Jerry744/halfmind-flow/capsule/structure_hat_v3 v1(Mirror).step

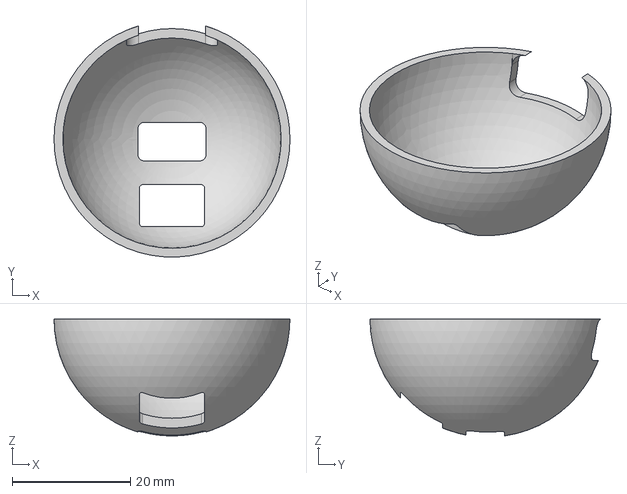
[picture p17: CAD file, 2025-07-03]
capsule/structure_hat_v3 v1(Mirror).step
40.0 x 39.1 x 19.8 mm
