Jerry744/halfmind-flow/capsule/structure_v1_shell.stp

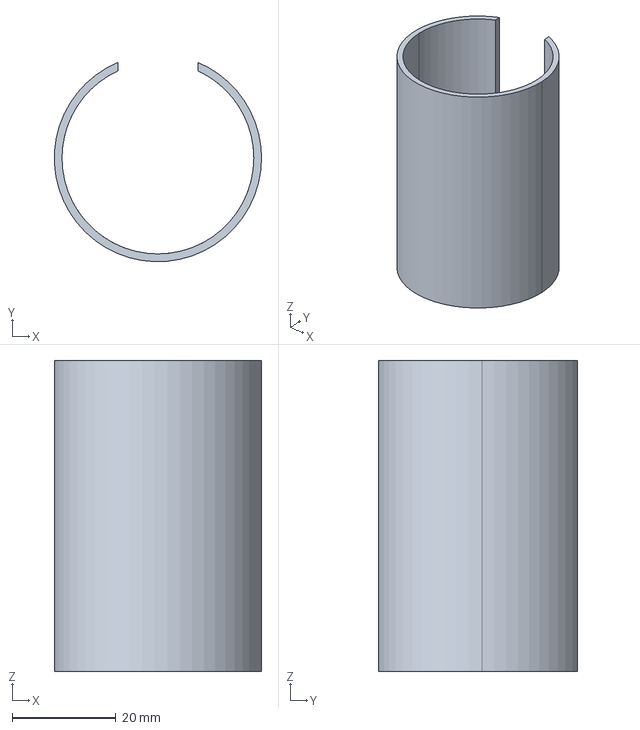
[picture p18: CAD file, 2025-07-01]
capsule/structure_v1_shell.stp
40.0 x 38.4 x 60.0 mm
