Jerry744/halfmind-flow/capsule/structure_hat_v3.stp

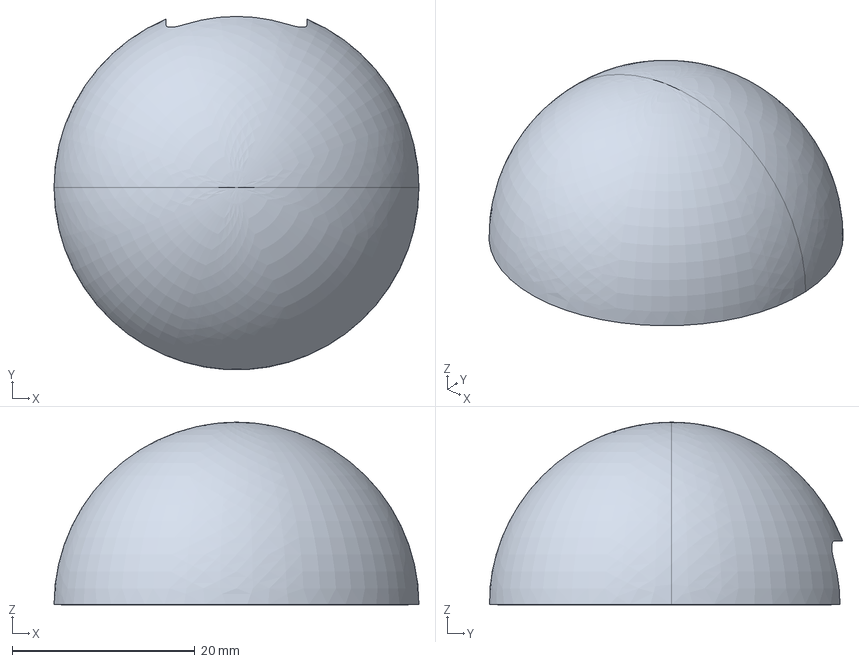
[picture p19: CAD file, 2025-07-01]
capsule/structure_hat_v3.stp
40.0 x 38.7 x 20.0 mm
