Jerry744/halfmind-flow/capsule/radar.stp

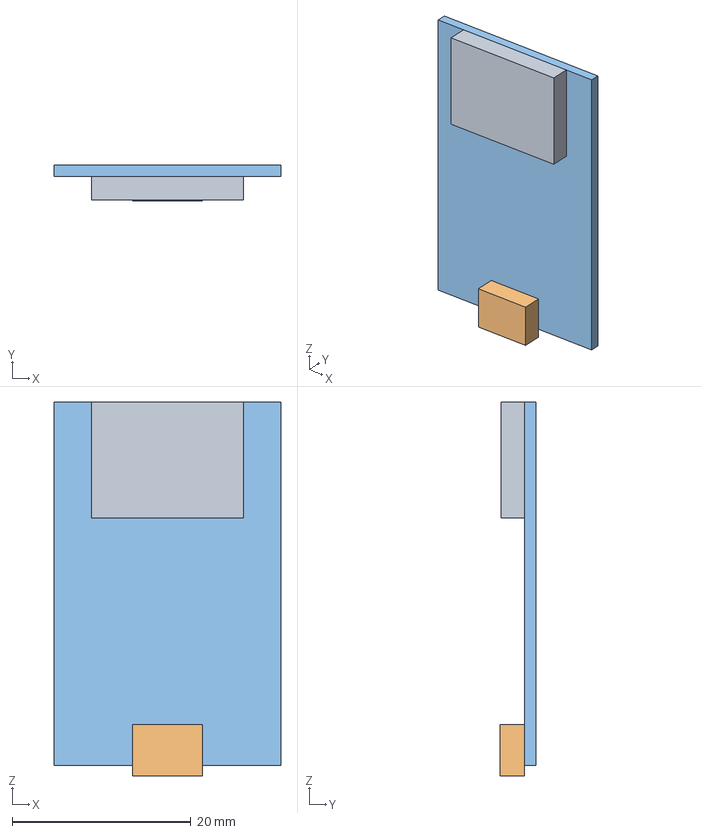
[picture p20: CAD file, 2025-07-01]
capsule/radar.stp
25.4 x 4.05 x 41.9 mm
