Jerry744/halfmind-flow/capsule/structure_v1.stp

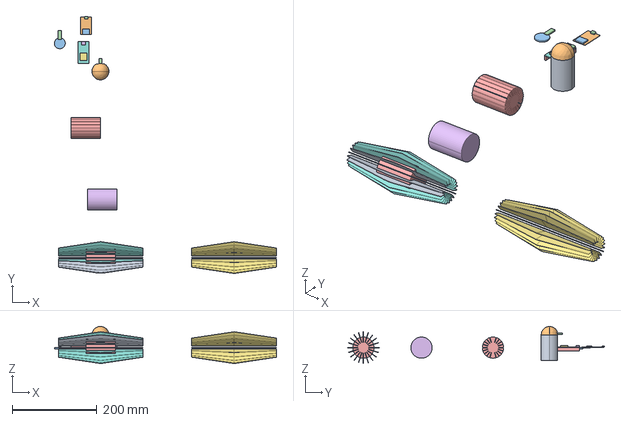
[picture p21: CAD file, 2025-07-01]
capsule/structure_v1.stp
523.6 x 605.5 x 87.5 mm
