Jerry744/halfmind-flow/capsule/led.stp

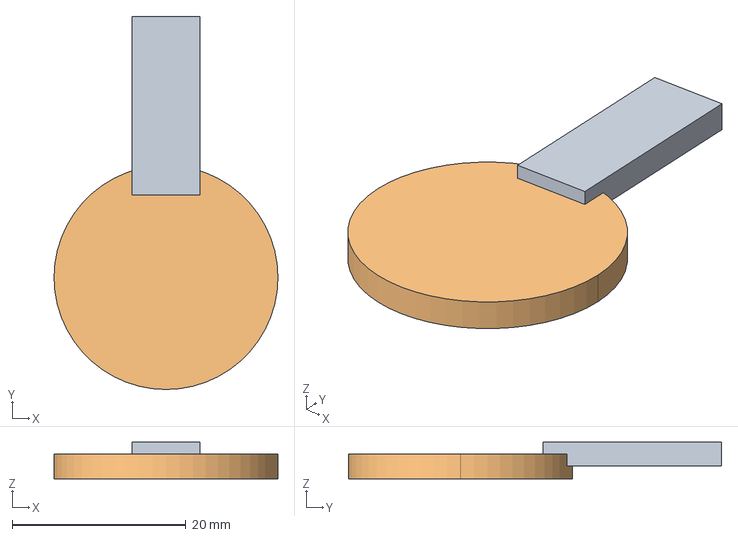
[picture p22: CAD file, 2025-07-01]
capsule/led.stp
25.8 x 42.9 x 4.20 mm
