Jerry744/halfmind-flow/capsule/esp32.stp

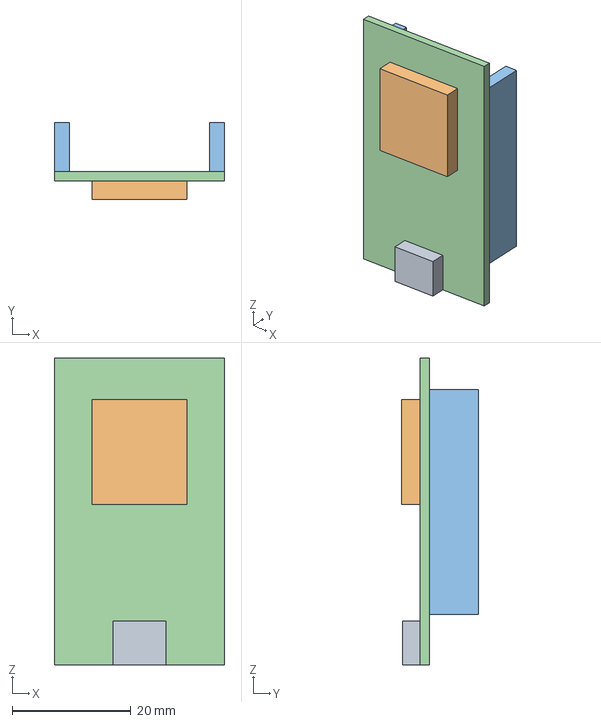
[picture p23: CAD file, 2025-07-01]
capsule/esp32.stp
28.6 x 12.9 x 51.6 mm
