Jerry744/halfmind-flow/capsule/structure_shell_v3.stp

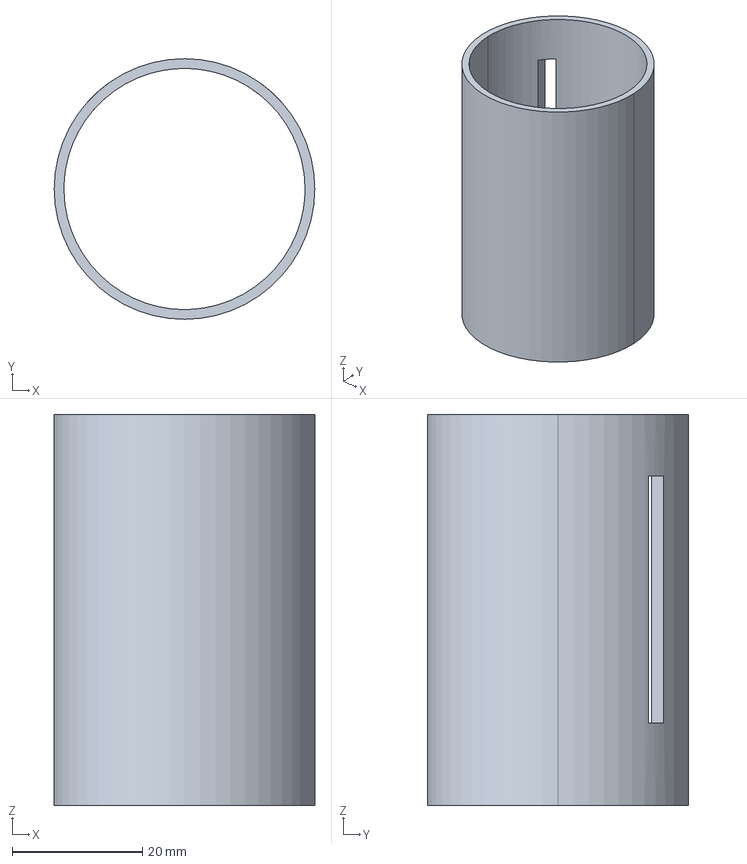
[picture p24: CAD file, 2025-07-01]
capsule/structure_shell_v3.stp
40.0 x 40.0 x 60.0 mm
