Jerry744/halfmind-flow/capsule/structure_v1_base.stp

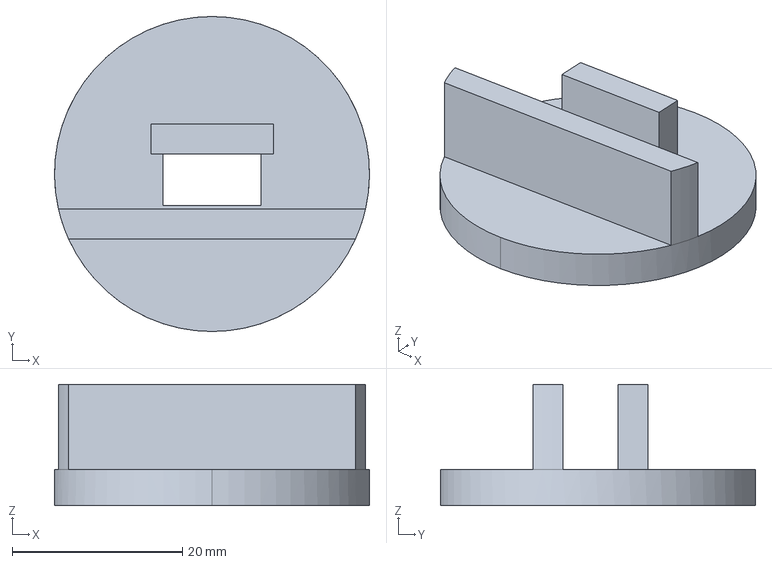
[picture p25: CAD file, 2025-07-01]
capsule/structure_v1_base.stp
37.0 x 37.0 x 14.2 mm
