Jerry744/halfmind-flow/capsule/structure_base_v3.stp

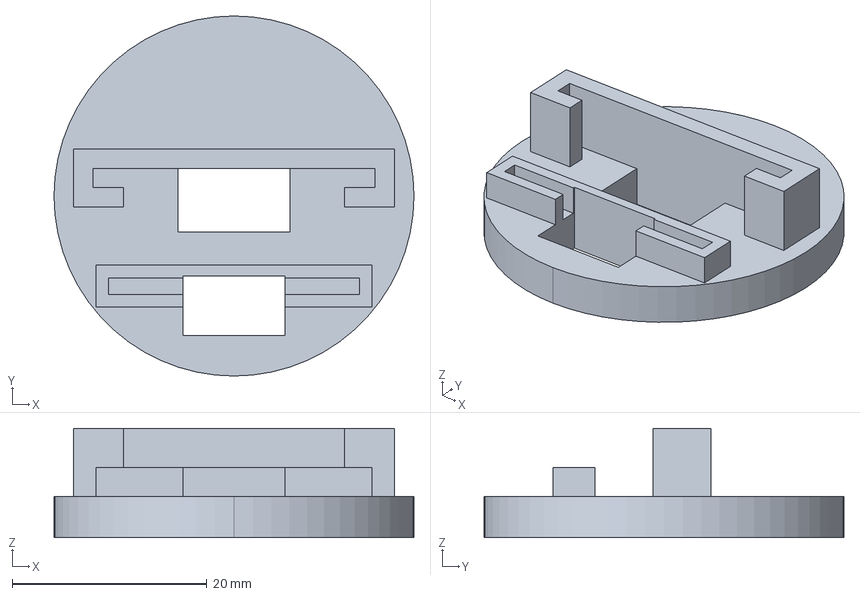
[picture p26: CAD file, 2025-07-01]
capsule/structure_base_v3.stp
37.0 x 37.0 x 11.2 mm
