Jerry744/halfmind-flow/arduino_esp32/MR60BHA1_human_existence_inf_output/MR60BHA1_human_existence_inf_output.ino

#include "Arduino.h"
#include <60ghzbreathheart.h>

#include <SoftwareSerial.h>
// Choose any two pins that can be used with SoftwareSerial to RX & TX
// #define RX_Pin A2
// #define TX_Pin A3
#define TX_Pin 1
#define RX_Pin 0

SoftwareSerial mySerial = SoftwareSerial(RX_Pin, TX_Pin);

// we'll be using software serial
BreathHeart_60GHz radar = BreathHeart_60GHz(&mySerial);

// can also try hardware serial with
// BreathHeart_60GHz radar = BreathHeart_60GHz(&Serial1);

void setup() {
  // put your setup code here, to run once:
  Serial.begin(115200);
  // Serial1.begin(115200);
  // mySerial.begin(115200);
  mySerial.begin(115200);
  while(!Serial);   //When the serial port is opened, the program starts to execute.
    mySerial.println("Readly");
}

void loop()
{
  // put your main code here, to run repeatedly:
  radar.recvRadarBytes();           //Receive radar data and start processing
  radar.showData();                 //Serial port prints a set of received data frames
  delay(500);                       //Add time delay to avoid program jam
  mySerial.println("Readly1");
}
